feklee/san/docs/notes/128a47a0-23ea-11e9-a8da-000c296198cf/images/2018-10-11+02_complete_set.jpg

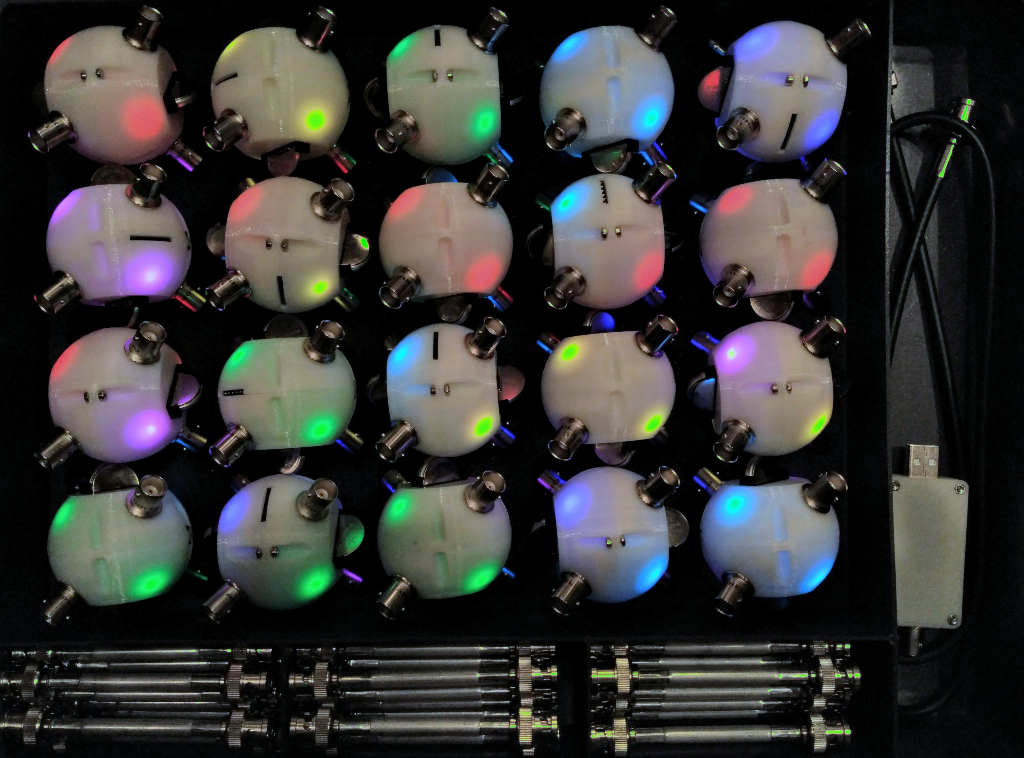
docs/notes/128a47a0-23ea-11e9-a8da-000c296198cf/images/2018-10-11+02_complete_set.jpg
