feklee/san/docs/notes/128a47a0-23ea-11e9-a8da-000c296198cf/images/ADXL337.jpg

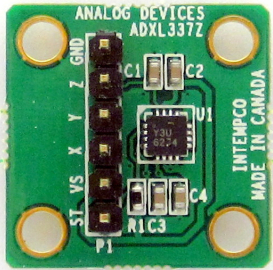
docs/notes/128a47a0-23ea-11e9-a8da-000c296198cf/images/ADXL337.jpg
