feklee/san/docs/notes/128a47a0-23ea-11e9-a8da-000c296198cf/images/web-audio-example.png

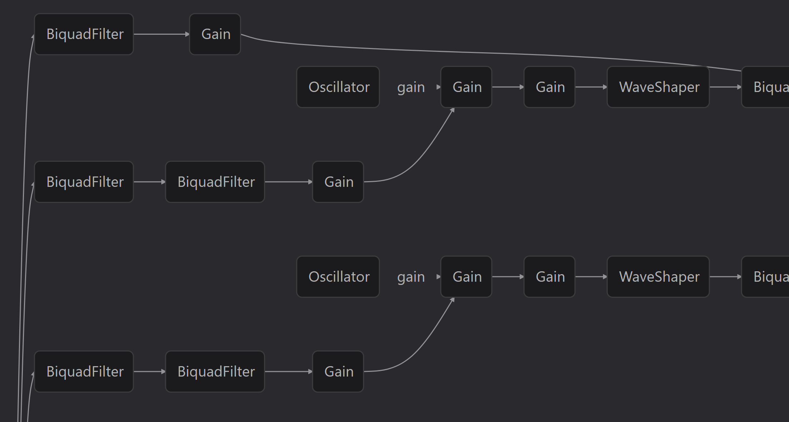
docs/notes/128a47a0-23ea-11e9-a8da-000c296198cf/images/web-audio-example.png
