feklee/san/hardware/desktop/usb_root_node/parts.jpg

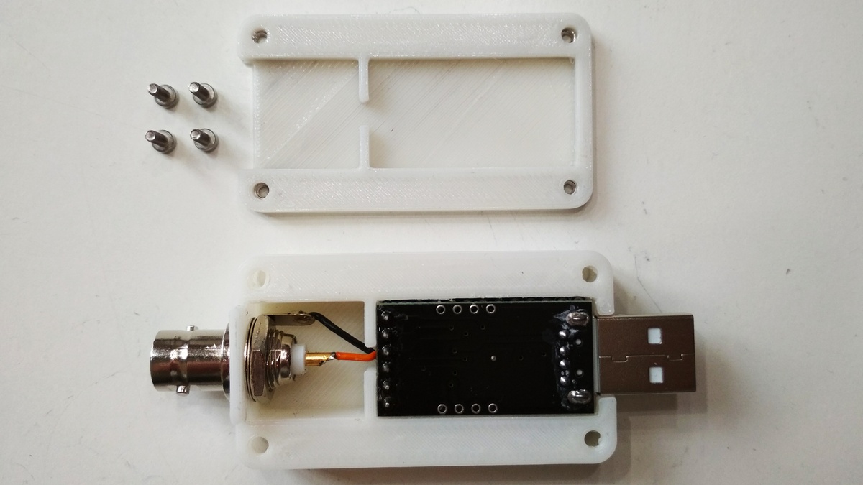
hardware/desktop/usb_root_node/parts.jpg
