feklee/san/hardware/life_size/nodes/components/main_pcb/Altium/main_board_back.png

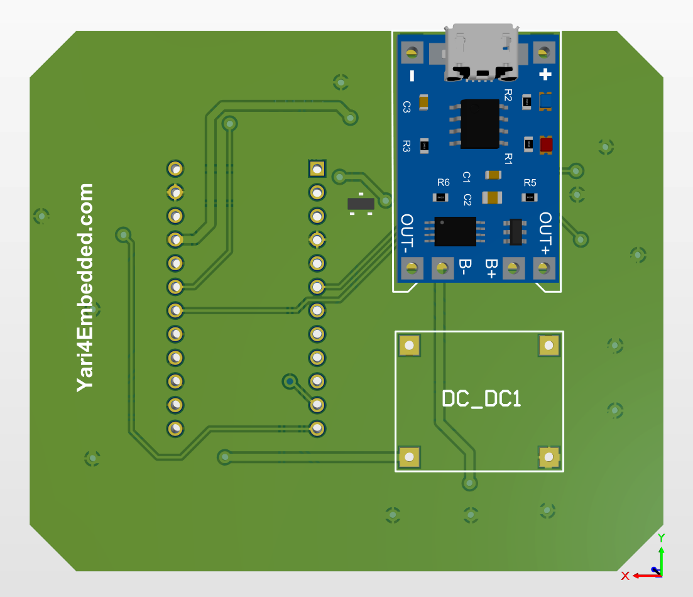
hardware/life_size/nodes/components/main_pcb/Altium/main_board_back.png
