feklee/san/hardware/life_size/nodes/components/main_pcb/Altium/main_board_dimentions.png

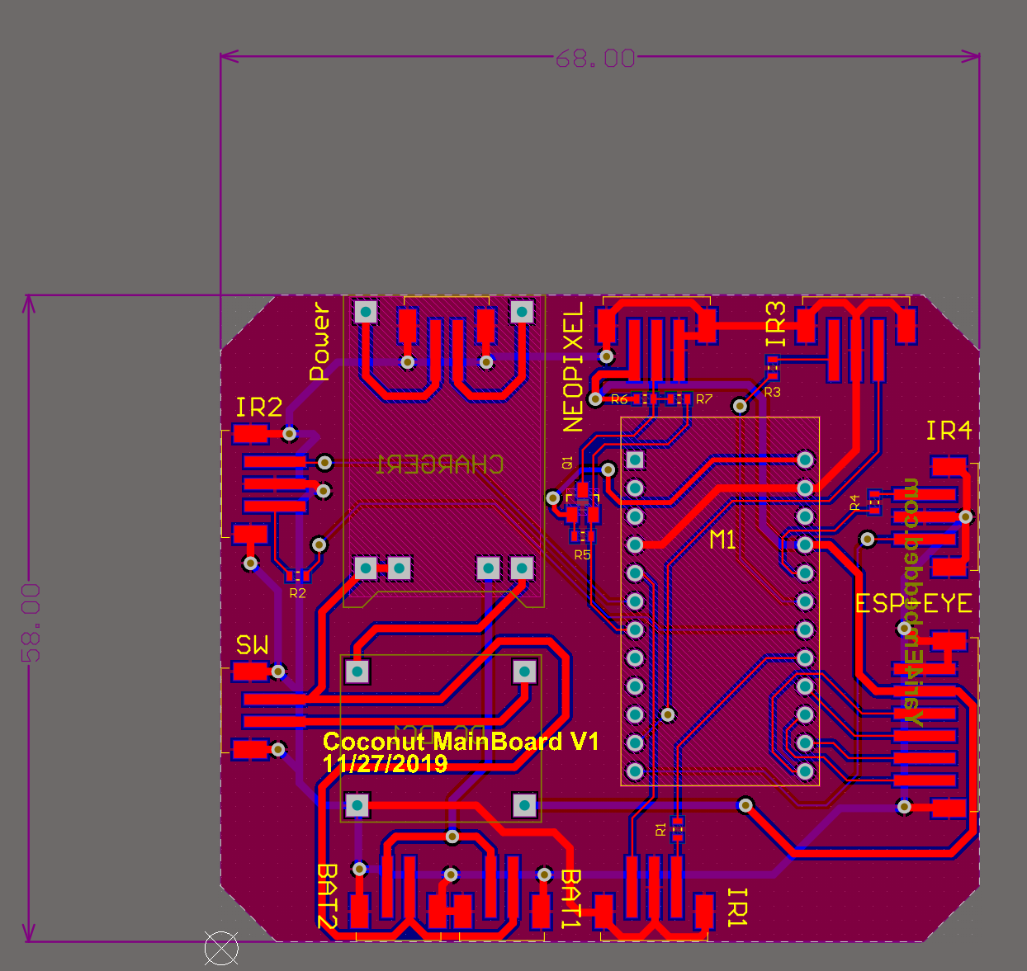
hardware/life_size/nodes/components/main_pcb/Altium/main_board_dimentions.png
