feklee/san/hardware/life_size/nodes/components/main_pcb/Altium/main_board_front.png

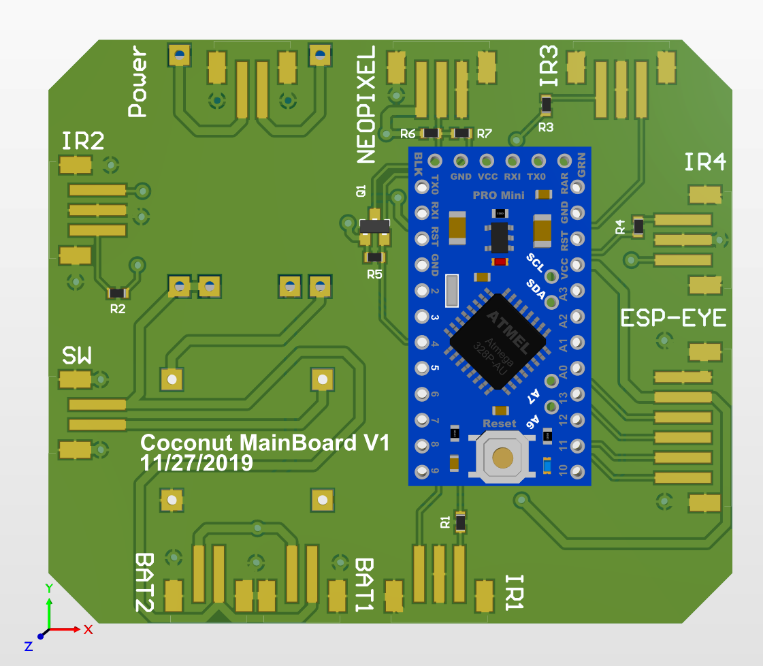
hardware/life_size/nodes/components/main_pcb/Altium/main_board_front.png
