feklee/san/hardware/life_size/nodes/components/port_pcb/Altium/ir_board_bottom.png

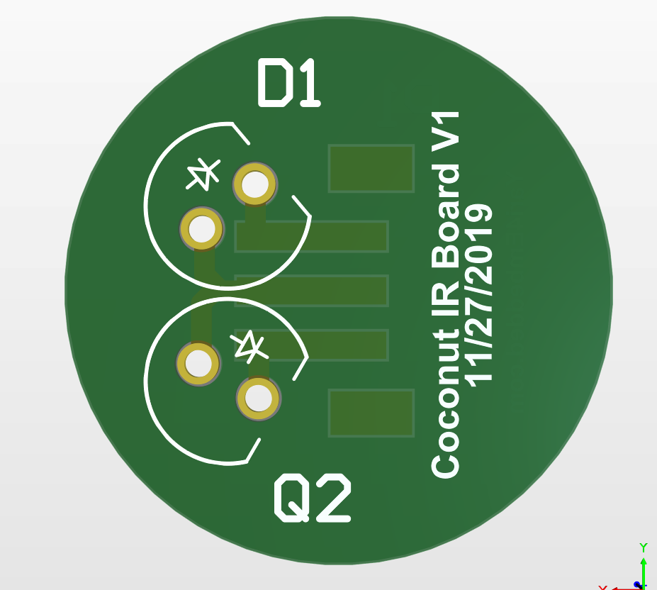
hardware/life_size/nodes/components/port_pcb/Altium/ir_board_bottom.png
