feklee/san/hardware/life_size/nodes/components/port_pcb/Altium/ir_board_dimensions.png

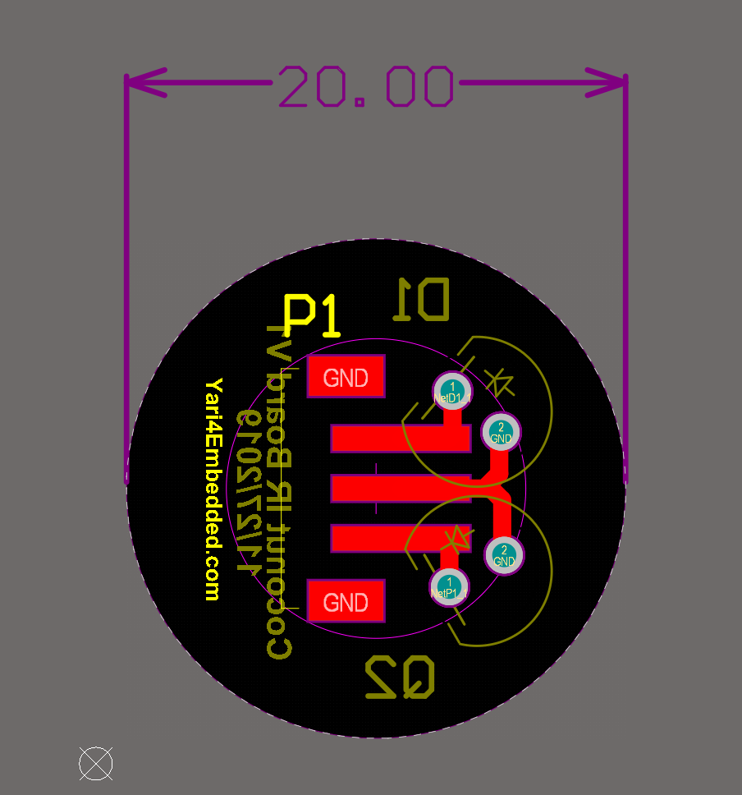
hardware/life_size/nodes/components/port_pcb/Altium/ir_board_dimensions.png
