feklee/san/hardware/desktop/nodes/LedTest/setup.jpg

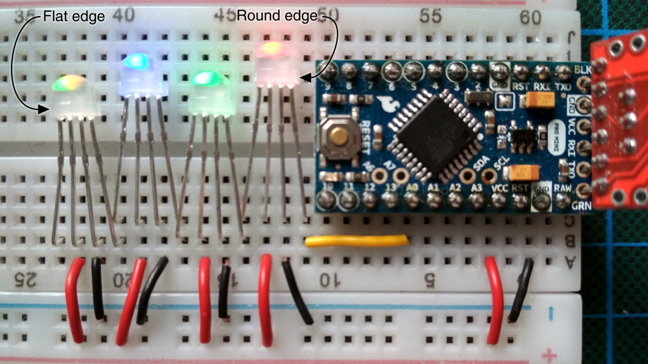
hardware/desktop/nodes/LedTest/setup.jpg
