feklee/san/hardware/desktop/usb_root_node/assembled.jpg

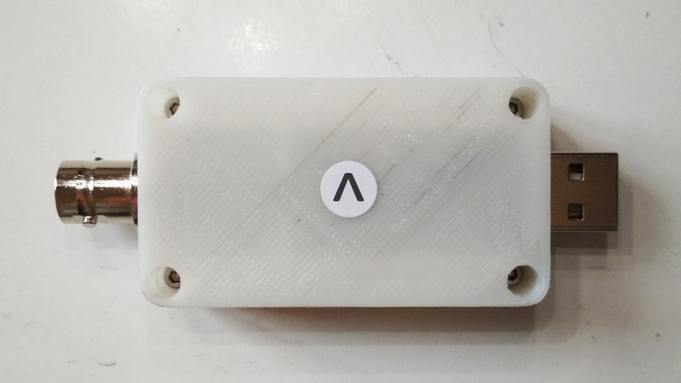
hardware/desktop/usb_root_node/assembled.jpg
