feklee/san/hardware/life_size/nodes/esp_server/main/app_httpd.c

// Copyright 2015-2016 Espressif Systems (Shanghai) PTE LTD, modified
// 2019 by Felix E. Klee <felix.klee@inka.de>
//
// Licensed under the Apache License, Version 2.0 (the "License");
// you may not use this file except in compliance with the License.
// You may obtain a copy of the License at
//
//     http://www.apache.org/licenses/LICENSE-2.0
//
// Unless required by applicable law or agreed to in writing, software
// distributed under the License is distributed on an "AS IS" BASIS,
// WITHOUT WARRANTIES OR CONDITIONS OF ANY KIND, either express or implied.
// See the License for the specific language governing permissions and
// limitations under the License.
#include "app_httpd.h"
#include "esp_http_server.h"
#include "esp_timer.h"
#include "esp_camera.h"
#include "img_converters.h"
#include "fb_gfx.h"
#include "sdkconfig.h"
#include "app_spi.h"

#if defined(ARDUINO_ARCH_ESP32) && defined(CONFIG_ARDUHAL_ESP_LOG)
#include "esp32-hal-log.h"
#define TAG ""
#else
#include "esp_log.h"
static const char* TAG = "httpd";
#endif

#if CONFIG_ESP_FACE_DETECT_ENABLED
#include "fd_forward.h"
#if CONFIG_ESP_FACE_RECOGNITION_ENABLED
#include "fr_forward.h"

#define ENROLL_CONFIRM_TIMES 5
#define FACE_ID_SAVE_NUMBER 7
#endif

#define FACE_COLOR_WHITE  0x00FFFFFF
#define FACE_COLOR_BLACK  0x00000000
#define FACE_COLOR_RED    0x000000FF
#define FACE_COLOR_GREEN  0x0000FF00
#define FACE_COLOR_BLUE   0x00FF0000
#define FACE_COLOR_YELLOW (FACE_COLOR_RED | FACE_COLOR_GREEN)
#define FACE_COLOR_CYAN   (FACE_COLOR_BLUE | FACE_COLOR_GREEN)
#define FACE_COLOR_PURPLE (FACE_COLOR_BLUE | FACE_COLOR_RED)
#endif

#define BUF_LEN 81

typedef struct {
        httpd_req_t *req;
        size_t len;
} jpg_chunking_t;

#define PART_BOUNDARY "123456789000000000000987654321"
static const char* _STREAM_CONTENT_TYPE = "multipart/x-mixed-replace;boundary=" PART_BOUNDARY;
static const char* _STREAM_BOUNDARY = "\r\n--" PART_BOUNDARY "\r\n";
static const char* _STREAM_PART = "Content-Type: image/jpeg\r\nContent-Length: %u\r\n\r\n";

httpd_handle_t stream_httpd = NULL;
httpd_handle_t camera_httpd = NULL;
#if CONFIG_ESP_FACE_DETECT_ENABLED
static mtmn_config_t mtmn_config = {0};
static int8_t detection_enabled = 0;
#if CONFIG_ESP_FACE_RECOGNITION_ENABLED
static int8_t recognition_enabled = 0;
static int8_t is_enrolling = 0;
static face_id_list id_list = {0};
#endif
#endif

typedef struct {
        size_t size; //number of values used for filtering
        size_t index; //current value index
        size_t count; //value count
        int sum;
        int * values; //array to be filled with values
} ra_filter_t;

static ra_filter_t ra_filter;

static ra_filter_t * ra_filter_init(ra_filter_t * filter, size_t sample_size){
    memset(filter, 0, sizeof(ra_filter_t));

    filter->values = (int *)malloc(sample_size * sizeof(int));
    if(!filter->values){
        return NULL;
    }
    memset(filter->values, 0, sample_size * sizeof(int));

    filter->size = sample_size;
    return filter;
}

static int ra_filter_run(ra_filter_t * filter, int value){
    if(!filter->values){
        return value;
    }
    filter->sum -= filter->values[filter->index];
    filter->values[filter->index] = value;
    filter->sum += filter->values[filter->index];
    filter->index++;
    filter->index = filter->index % filter->size;
    if (filter->count < filter->size) {
        filter->count++;
    }
    return filter->sum / filter->count;
}

#if CONFIG_ESP_FACE_DETECT_ENABLED
#if CONFIG_ESP_FACE_RECOGNITION_ENABLED
static void rgb_print(dl_matrix3du_t *image_matrix, uint32_t color, const char * str){
    fb_data_t fb;
    fb.width = image_matrix->w;
    fb.height = image_matrix->h;
    fb.data = image_matrix->item;
    fb.bytes_per_pixel = 3;
    fb.format = FB_BGR888;
    fb_gfx_print(&fb, (fb.width - (strlen(str) * 14)) / 2, 10, color, str);
}

static int rgb_printf(dl_matrix3du_t *image_matrix, uint32_t color, const char *format, ...)
{
    char loc_buf[64];
    char * temp = loc_buf;
    int len;
    va_list arg;
    va_list copy;
    va_start(arg, format);
    va_copy(copy, arg);
    len = vsnprintf(loc_buf, sizeof(loc_buf), format, arg);
    va_end(copy);
    if(len >= sizeof(loc_buf)){
        temp = (char*)malloc(len+1);
        if(temp == NULL) {
            return 0;
        }
    }
    vsnprintf(temp, len+1, format, arg);
    va_end(arg);
    rgb_print(image_matrix, color, temp);
    if(len > 64){
        free(temp);
    }
    return len;
}
#endif
static void draw_face_boxes(dl_matrix3du_t *image_matrix, box_array_t *boxes, int face_id){
    int x, y, w, h, i;
    uint32_t color = FACE_COLOR_YELLOW;
    if(face_id < 0){
        color = FACE_COLOR_RED;
    } else if(face_id > 0){
        color = FACE_COLOR_GREEN;
    }
    fb_data_t fb;
    fb.width = image_matrix->w;
    fb.height = image_matrix->h;
    fb.data = image_matrix->item;
    fb.bytes_per_pixel = 3;
    fb.format = FB_BGR888;
    for (i = 0; i < boxes->len; i++){
        // rectangle box
        x = (int)boxes->box[i].box_p[0];
        y = (int)boxes->box[i].box_p[1];
        w = (int)boxes->box[i].box_p[2] - x + 1;
        h = (int)boxes->box[i].box_p[3] - y + 1;
        fb_gfx_drawFastHLine(&fb, x, y, w, color);
        fb_gfx_drawFastHLine(&fb, x, y+h-1, w, color);
        fb_gfx_drawFastVLine(&fb, x, y, h, color);
        fb_gfx_drawFastVLine(&fb, x+w-1, y, h, color);
#if 0
        // landmark
        int x0, y0, j;
        for (j = 0; j < 10; j+=2) {
            x0 = (int)boxes->landmark[i].landmark_p[j];
            y0 = (int)boxes->landmark[i].landmark_p[j+1];
            fb_gfx_fillRect(&fb, x0, y0, 3, 3, color);
        }
#endif
    }
}

#if CONFIG_ESP_FACE_RECOGNITION_ENABLED
static int run_face_recognition(dl_matrix3du_t *image_matrix, box_array_t *net_boxes){
    dl_matrix3du_t *aligned_face = NULL;
    int matched_id = 0;

    aligned_face = dl_matrix3du_alloc(1, FACE_WIDTH, FACE_HEIGHT, 3);
    if(!aligned_face){
        ESP_LOGE(TAG, "Could not allocate face recognition buffer");
        return matched_id;
    }
    if (align_face(net_boxes, image_matrix, aligned_face) == ESP_OK){
        if (is_enrolling == 1){
            int8_t left_sample_face = enroll_face(&id_list, aligned_face);

            if(left_sample_face == (ENROLL_CONFIRM_TIMES - 1)){
                ESP_LOGD(TAG, "Enrolling Face ID: %d", id_list.tail);
            }
            ESP_LOGD(TAG, "Enrolling Face ID: %d sample %d", id_list.tail, ENROLL_CONFIRM_TIMES - left_sample_face);
            rgb_printf(image_matrix, FACE_COLOR_CYAN, "ID[%u] Sample[%u]", id_list.tail, ENROLL_CONFIRM_TIMES - left_sample_face);
            if (left_sample_face == 0){
                is_enrolling = 0;
                ESP_LOGD(TAG, "Enrolled Face ID: %d", id_list.tail);
            }
        } else {
            matched_id = recognize_face(&id_list, aligned_face);
            if (matched_id >= 0) {
                ESP_LOGW(TAG, "Match Face ID: %u", matched_id);
                rgb_printf(image_matrix, FACE_COLOR_GREEN, "Hello Subject %u", matched_id);
            } else {
                ESP_LOGW(TAG, "No Match Found");
                rgb_print(image_matrix, FACE_COLOR_RED, "Intruder Alert!");
                matched_id = -1;
            }
        }
    } else {
        ESP_LOGW(TAG, "Face Not Aligned");
        //rgb_print(image_matrix, FACE_COLOR_YELLOW, "Human Detected");
    }

    dl_matrix3du_free(aligned_face);
    return matched_id;
}
#endif
#endif

static esp_err_t stream_handler(httpd_req_t *req){
    camera_fb_t * fb = NULL;
    esp_err_t res = ESP_OK;
    size_t _jpg_buf_len = 0;
    uint8_t * _jpg_buf = NULL;
    char * part_buf[64];
#if CONFIG_ESP_FACE_DETECT_ENABLED
    dl_matrix3du_t *image_matrix = NULL;
    bool detected = false;
    int face_id = 0;
    int64_t fr_start = 0;
    int64_t fr_ready = 0;
    int64_t fr_face = 0;
    int64_t fr_recognize = 0;
    int64_t fr_encode = 0;
#endif

    static int64_t last_frame = 0;
    if(!last_frame) {
        last_frame = esp_timer_get_time();
    }

    res = httpd_resp_set_type(req, _STREAM_CONTENT_TYPE);
    if(res != ESP_OK){
        return res;
    }

    httpd_resp_set_hdr(req, "Access-Control-Allow-Origin", "*");

    while(true){
        fb = esp_camera_fb_get();
        if (!fb) {
            ESP_LOGE(TAG, "Camera capture failed");
            res = ESP_FAIL;
        } else {
#if CONFIG_ESP_FACE_DETECT_ENABLED
            fr_start = esp_timer_get_time();
            fr_ready = fr_start;
            fr_face = fr_start;
            fr_encode = fr_start;
            fr_recognize = fr_start;
            if(!detection_enabled || fb->width > 400){
#endif
                if(fb->format != PIXFORMAT_JPEG){
                    bool jpeg_converted = frame2jpg(fb, 80, &_jpg_buf, &_jpg_buf_len);
                    esp_camera_fb_return(fb);
                    fb = NULL;
                    if(!jpeg_converted){
                        ESP_LOGE(TAG, "JPEG compression failed");
                        res = ESP_FAIL;
                    }
                } else {
                    _jpg_buf_len = fb->len;
                    _jpg_buf = fb->buf;
                }
#if CONFIG_ESP_FACE_DETECT_ENABLED
            } else {

                image_matrix = dl_matrix3du_alloc(1, fb->width, fb->height, 3);

                if (!image_matrix) {
                    ESP_LOGE(TAG, "dl_matrix3du_alloc failed");
                    res = ESP_FAIL;
                } else {
                    if(!fmt2rgb888(fb->buf, fb->len, fb->format, image_matrix->item)){
                        ESP_LOGE(TAG, "fmt2rgb888 failed");
                        res = ESP_FAIL;
                    } else {
                        fr_ready = esp_timer_get_time();
                        box_array_t *net_boxes = NULL;
                        if(detection_enabled){
                            net_boxes = face_detect(image_matrix, &mtmn_config);
                        }
                        fr_face = esp_timer_get_time();
                        fr_recognize = fr_face;
                        if (net_boxes || fb->format != PIXFORMAT_JPEG){
                            if(net_boxes){
                                detected = true;
#if CONFIG_ESP_FACE_RECOGNITION_ENABLED
                                if(recognition_enabled){
                                    face_id = run_face_recognition(image_matrix, net_boxes);
                                }
                                fr_recognize = esp_timer_get_time();
#endif
                                draw_face_boxes(image_matrix, net_boxes, face_id);
                                dl_lib_free(net_boxes->score);
                                dl_lib_free(net_boxes->box);
                                dl_lib_free(net_boxes->landmark);
                                dl_lib_free(net_boxes);
                            }
                            if(!fmt2jpg(image_matrix->item, fb->width*fb->height*3, fb->width, fb->height, PIXFORMAT_RGB888, 90, &_jpg_buf, &_jpg_buf_len)){
                                ESP_LOGE(TAG, "fmt2jpg failed");
                            }
                            esp_camera_fb_return(fb);
                            fb = NULL;
                        } else {
                            _jpg_buf = fb->buf;
                            _jpg_buf_len = fb->len;
                        }
                        fr_encode = esp_timer_get_time();
                    }
                    dl_matrix3du_free(image_matrix);
                }
            }
#endif
        }
        if(res == ESP_OK){
            size_t hlen = snprintf((char *)part_buf, 64, _STREAM_PART, _jpg_buf_len);
            res = httpd_resp_send_chunk(req, (const char *)part_buf, hlen);
        }
        if(res == ESP_OK){
            res = httpd_resp_send_chunk(req, (const char *)_jpg_buf, _jpg_buf_len);
        }
        if(res == ESP_OK){
            res = httpd_resp_send_chunk(req, _STREAM_BOUNDARY, strlen(_STREAM_BOUNDARY));
        }
        if(fb){
            esp_camera_fb_return(fb);
            fb = NULL;
            _jpg_buf = NULL;
        } else if(_jpg_buf){
            free(_jpg_buf);
            _jpg_buf = NULL;
        }
        if(res != ESP_OK){
            break;
        }
        int64_t fr_end = esp_timer_get_time();

#if CONFIG_ESP_FACE_DETECT_ENABLED
        int64_t ready_time = (fr_ready - fr_start)/1000;
        int64_t face_time = (fr_face - fr_ready)/1000;
        int64_t recognize_time = (fr_recognize - fr_face)/1000;
        int64_t encode_time = (fr_encode - fr_recognize)/1000;
        int64_t process_time = (fr_encode - fr_start)/1000;
#endif

        int64_t frame_time = fr_end - last_frame;
        last_frame = fr_end;
        frame_time /= 1000;
        uint32_t avg_frame_time = ra_filter_run(&ra_filter, frame_time);
#if 0 // disable logging (too much info)
        ESP_LOGI(TAG, "MJPG: %uB %ums (%.1ffps), AVG: %ums (%.1ffps)"
#if CONFIG_ESP_FACE_DETECT_ENABLED
            ", %u+%u+%u+%u=%u %s%d"
#endif
            ,(uint32_t)(_jpg_buf_len),
            (uint32_t)frame_time, 1000.0 / (uint32_t)frame_time,
            avg_frame_time, 1000.0 / avg_frame_time
#if CONFIG_ESP_FACE_DETECT_ENABLED
            ,(uint32_t)ready_time, (uint32_t)face_time, (uint32_t)recognize_time, (uint32_t)encode_time, (uint32_t)process_time,
            (detected)?"DETECTED ":"", face_id
#endif
        );
#endif
    }


#ifdef CONFIG_LED_ILLUMINATOR_ENABLED
    isStreaming = false;
    enable_led(false);
#endif

    last_frame = 0;
    return res;
}

static bool evaluate_color_command(const char * const buf) {
    const char *c = buf + 1;
    char data[5] = {'C', 0};
    for (short i = 0; i < 4; i++) {
        char color = 0;
        for (short j = 0; j < 3; j++) {
            color <<= 2;
            int value = *c - 48;
            const bool value_is_valid = value >= 0 && value <= 3;
            if (!value_is_valid) {
                return false;
            }
            color += value;
            c++;
        }
        data[i + 1] = color;
    }
    app_spi_send(data, sizeof(data));
    return true;
}

static esp_err_t cmd_handler(httpd_req_t *req)
{
    char buf[BUF_LEN] = {'\0'};

    if (httpd_req_get_url_query_str(req, buf, BUF_LEN - 1) != ESP_OK) {
        httpd_resp_send_404(req);
        return ESP_FAIL;
    }

    const bool is_color_command = buf[0] == 'C' && strlen(buf) == 13;
    if (!is_color_command) {
        return httpd_resp_send_500(req);
    }

    bool success = evaluate_color_command(buf);
    if (!success) {
        return httpd_resp_send_500(req);
    }

    return httpd_resp_send(req, NULL, 0);
}

void app_httpd_main(){
    httpd_config_t config = HTTPD_DEFAULT_CONFIG();

    httpd_uri_t cmd_uri = {
        .uri = "/",
        .method = HTTP_GET,
        .handler = cmd_handler,
        .user_ctx = NULL
    };

    httpd_uri_t stream_uri = {
        .uri       = "/",
        .method    = HTTP_GET,
        .handler   = stream_handler,
        .user_ctx  = NULL
    };

    ra_filter_init(&ra_filter, 20);
#if CONFIG_ESP_FACE_DETECT_ENABLED
    mtmn_config.type = FAST;
    mtmn_config.min_face = 80;
    mtmn_config.pyramid = 0.707;
    mtmn_config.pyramid_times = 4;
    mtmn_config.p_threshold.score = 0.6;
    mtmn_config.p_threshold.nms = 0.7;
    mtmn_config.p_threshold.candidate_number = 20;
    mtmn_config.r_threshold.score = 0.7;
    mtmn_config.r_threshold.nms = 0.7;
    mtmn_config.r_threshold.candidate_number = 10;
    mtmn_config.o_threshold.score = 0.7;
    mtmn_config.o_threshold.nms = 0.7;
    mtmn_config.o_threshold.candidate_number = 1;
#if CONFIG_ESP_FACE_RECOGNITION_ENABLED
    face_id_init(&id_list, FACE_ID_SAVE_NUMBER, ENROLL_CONFIRM_TIMES);
#endif
#endif
    ESP_LOGI(TAG, "Starting web server on port: '%d'", config.server_port);
    if (httpd_start(&camera_httpd, &config) == ESP_OK)
    {
        httpd_register_uri_handler(camera_httpd, &cmd_uri);
    }

    config.server_port += 1;
    config.ctrl_port += 1;

    ESP_LOGI(TAG, "Starting stream server on port: '%d'", config.server_port);
    if (httpd_start(&stream_httpd, &config) == ESP_OK) {
        httpd_register_uri_handler(stream_httpd, &stream_uri);
    }
}
