feklee/san/hardware/life_size/nodes/esp_server/main/app_main.c

/* ESPRESSIF MIT License
 * 
 * Copyright (c) 2018 <ESPRESSIF SYSTEMS (SHANGHAI) PTE LTD>
 * 
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
 * THE SOFTWARE IS PROVIDED "AS IS", WITHOUT WARRANTY OF ANY KIND, EXPRESS OR
 * IMPLIED, INCLUDING BUT NOT LIMITED TO THE WARRANTIES OF MERCHANTABILITY, FITNESS
 * FOR A PARTICULAR PURPOSE AND NONINFRINGEMENT. IN NO EVENT SHALL THE AUTHORS OR
 * COPYRIGHT HOLDERS BE LIABLE FOR ANY CLAIM, DAMAGES OR OTHER LIABILITY, WHETHER
 * IN AN ACTION OF CONTRACT, TORT OR OTHERWISE, ARISING FROM, OUT OF OR IN
 * CONNECTION WITH THE SOFTWARE OR THE USE OR OTHER DEALINGS IN THE SOFTWARE.
 */

#include "app_camera.h"
#include "app_wifi.h"
#include "app_httpd.h"
#include "app_spi.h"

void app_main()
{
    app_wifi_main();
    app_camera_main();
    app_httpd_main();
    app_spi_main();
}
