feklee/san/hardware/life_size/nodes/ArduinoFirmware/spiTransfer.cpp

#include <SPI.h>
#include "spiTransfer.h"

char spiRxBuffer[spiBufferLength];
char spiTxBuffer[spiBufferLength];

void spiTransferSetup() {
  SPI.begin();
  SPI.setDataMode(SPI_MODE1); // mode 1 seems to be more stable than mode 3
}

void clearSpiTxBuffer() {
  memset(spiTxBuffer, '\0', spiBufferLength);
}

void doSpiTransfer() {
  digitalWrite(SS, LOW);
  for (int i = 0; i < spiBufferLength; i++) {
    char txByte = spiTxBuffer[i];
    char rxByte = SPI.transfer(txByte);
    spiRxBuffer[i] = rxByte;
  }
  digitalWrite(SS, HIGH);
}
