feklee/san/hardware/life_size/nodes/ArduinoFirmware/pairMessageQueue.cpp

#include "pairMessageQueue.h"
#include "message.h"
#include "settings.h"

static uint8_t first = 0;
static uint8_t last = 0;
static uint8_t length = 0;
static byte buffer[maxPairMessageQueueSize][pairMessageSize];

static void incrementPosition(uint8_t &position) {
  position = (position + 1) % maxPairMessageQueueSize;
}

static void decrementLength() {
  length = (length > 0) ? length - 1 : 0;
}

void enqueuePairMessage(const byte *pairMessage) {
  memcpy(buffer[last], pairMessage, pairMessageSize);
  incrementPosition(last);

  if (length < maxPairMessageQueueSize) {
    length++;
  } else {
    incrementPosition(first);
  }
}

// don't call when queue is empty
const byte *dequeuePairMessage() {
  const byte *pairMessage = buffer[first];
  incrementPosition(first);
  decrementLength();
  return pairMessage;
}

void clearPairMessageQueue() {
  first = 0;
  last = 0;
  length = 0;
}

uint8_t numberOfQueuedPairMessages() {
  return length;
}
