feklee/san/hardware/desktop/nodes/Firmware/colors.h

#pragma once

const byte black[] = {0, 0, 0};
const byte gray[] = {0x80, 0x80, 0x80};
const byte white[] = {0xff, 0xff, 0xff};
const byte red[] = {0xff, 0, 0};
const byte yellow[] = {0xff, 0xff, 0};
const byte lime[] = {0, 0xff, 0};
const byte aqua[] = {0, 0xff, 0xff};
const byte blue[] = {0, 0, 0xff};
const byte fuchsia[] = {0xff, 0, 0xff};
